hixfield/HixCO2TemperatureIRBlaster/doc/powered_up.jpg

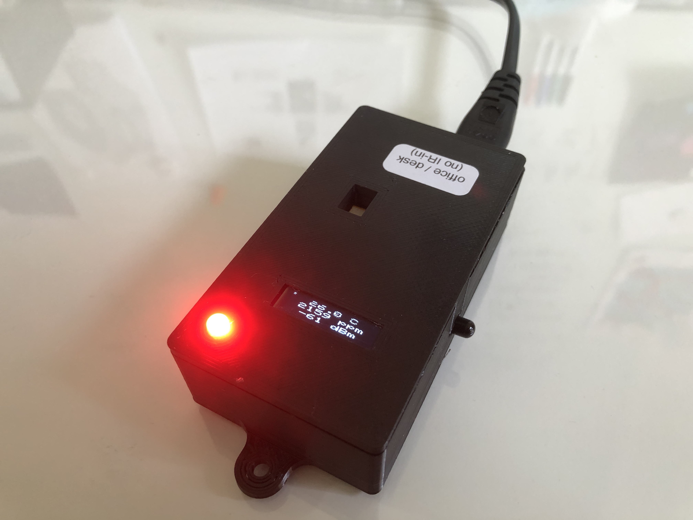
doc/powered_up.jpg
