hixfield/HixCO2TemperatureIRBlaster/software/src/secret.cpp

#include "secret.h"

/*

Fill in your details and uncomment this whole section


const char * Secret::WIFI_SSID   = "xxxxxxxxxx";
const char * Secret::WIFI_PWD    = "xxxxxxxxxx";
const char * Secret::MQTT_SERVER = "xxxxxxxxxx";
const char * Secret::CONFIG_PWD   = "bornem1973";

*/
