hixfield/HixCO2TemperatureIRBlaster/software/src/secret.h

#ifndef Secret_h
#define Secret_h


class Secret {
  public:
    static const char * WIFI_SSID;
    static const char * WIFI_PWD;
    static const char * MQTT_SERVER;
    static const char * CONFIG_PWD;
};

#endif
